joeji073/FD3S-DIGITAL-GAUGE-CLUSTER/FINAL_CENTER/gaugeassets2.h

// This file was generated with the command-line:
//    gd3asset -o gaugeassets2.h numberfont.ttf,size=70 numberfont2.ttf,size=25 GAUGENEEDLE.png,format=ARGB1555 REDNEEDLE.png,format=ARGB1555

#define NUMBERFONT_HANDLE 0
#define NUMBERFONT_WIDTH 71
#define NUMBERFONT_HEIGHT 77
#define NUMBERFONT_CELLS 96
#define NUMBERFONT2_HANDLE 1
#define NUMBERFONT2_WIDTH 26
#define NUMBERFONT2_HEIGHT 28
#define NUMBERFONT2_CELLS 96
#define GAUGENEEDLE_HANDLE 2
#define GAUGENEEDLE_WIDTH 70
#define GAUGENEEDLE_HEIGHT 70
#define GAUGENEEDLE_CELLS 1
#define REDNEEDLE_HANDLE 3
#define REDNEEDLE_WIDTH 90
#define REDNEEDLE_HEIGHT 25
#define REDNEEDLE_CELLS 1
#define ASSETS_END 315652UL
static const PROGMEM uint8_t __assets[31408] = {
0, 0, 0, 5, 0, 0, 0, 1, 77, 142, 0, 8, 0, 0, 0, 41, 77, 72, 16, 7, 0,
0, 0, 40, 128, 165, 126, 1, 43, 255, 255, 255, 0, 0, 0, 0, 128, 15, 4,
0, 1, 0, 0, 5, 20, 16, 4, 1, 28, 52, 0, 8, 0, 0, 0, 41, 28, 26, 16, 7,
0, 0, 0, 40, 148, 226, 3, 1, 43, 255, 255, 255, 1, 0, 0, 0, 148, 152,
4, 0, 2, 0, 0, 5, 40, 153, 4, 1, 70, 140, 0, 8, 0, 0, 0, 41, 70, 24,
1, 7, 0, 0, 0, 40, 3, 0, 0, 5, 112, 191, 4, 1, 25, 180, 0, 8, 0, 0, 0,
41, 25, 104, 1, 7, 0, 0, 0, 40, 34, 255, 255, 255, 0, 0, 0, 0, 120,
218, 236, 189, 9, 124, 108, 89, 85, 47, 92, 243, 92, 149, 92, 102,
186, 233, 36, 52, 32, 131, 244, 173, 56, 32, 126, 63, 164, 43, 248,
176, 197, 169, 43, 234, 19, 81, 180, 43, 190, 135, 162, 50, 84, 84,
236, 198, 207, 39, 21, 121, 14, 253, 4, 187, 130, 62, 249, 126, 202,
80, 1, 31, 138, 19, 21, 158, 126, 8, 10, 93, 1, 69, 6, 219, 174, 0,
234, 99, 250, 186, 210, 221, 50, 116, 55, 247, 158, 123, 111, 110,
110, 134, 74, 234, 124, 103, 216, 211, 201, 61, 107, 128, 84, 135, 59,
156, 245, 107, 232, 206, 189, 59, 85, 231, 236, 189, 246, 90, 255,
245, 95, 107, 175, 29, 139, 69, 18, 73, 36, 145, 68, 18, 73, 36, 145,
68, 18, 73, 36, 151, 172, 100, 108, 71, 246, 25, 99, 118, 241, 49, 89,
119, 204, 5, 198, 152, 243, 248, 152, 156, 59, 230, 44, 99, 204, 58,
62, 38, 239, 142, 89, 97, 140, 89, 196, 199, 20, 220, 49, 115, 140,
49, 51, 248, 152, 162, 51, 100, 20, 163, 199, 12, 137, 49, 37, 103,
204, 14, 99, 204, 22, 49, 166, 236, 140, 57, 199, 24, 179, 65, 140,
169, 56, 99, 214, 24, 99, 150, 137, 49, 19, 206, 152, 5, 198, 152, 89,
98, 204, 52, 61, 205, 238, 152, 125, 106, 76, 213, 182, 247, 24, 99,
182, 169, 49, 53, 82, 227, 189, 49, 103, 169, 49, 117, 82, 227, 189,
49, 43, 212, 152, 6, 169, 241, 222, 152, 121, 106, 76, 147, 212, 120,
119, 12, 185, 20, 177, 22, 169, 241, 238, 152, 29, 114, 76, 155, 212,
120, 119, 204, 38, 57, 166, 67, 106, 188, 59, 102, 141, 28, 211, 37,
53, 222, 29, 179, 64, 142, 233, 145, 26, 239, 142, 153, 36, 199, 244,
15, 46, 55, 207, 212, 178, 105, 147, 208, 113, 199, 204, 83, 179, 76,
155, 141, 62, 195, 130, 15, 220, 49, 196, 51, 91, 206, 16, 98, 162,
227, 12, 135, 155, 116, 199, 16, 230, 39, 205, 112, 202, 158, 227,
222, 142, 69, 18, 201, 213, 36, 30, 62, 156, 75, 185, 255, 191, 132,
97, 182, 145, 191, 65, 102, 49, 60, 182, 231, 161, 214, 17, 138, 145,
182, 60, 36, 185, 139, 226, 159, 123, 189, 111, 220, 194, 48, 137,
189, 234, 33, 183, 123, 49, 188, 225, 24, 196, 178, 55, 18, 193, 0,
142, 33, 195, 209, 84, 211, 51, 64, 85, 212, 228, 181, 60, 152, 89,
67, 77, 149, 99, 125, 55, 61, 180, 176, 131, 90, 223, 117, 239, 27,
55, 81, 235, 187, 236, 122, 103, 12, 225, 12, 60, 59, 223, 65, 129,
164, 229, 173, 83, 15, 195, 235, 113, 223, 174, 14, 48, 100, 146, 244,
3, 25, 11, 179, 192, 105, 15, 178, 197, 209, 144, 39, 227, 33, 227, 4,
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
};
#define LOAD_ASSETS()  (GD.copy(__assets, sizeof(__assets)), GD.loadptr = ASSETS_END)
static const shape_t NUMBERFONT_SHAPE = {0, 71, 77, 0};
static const shape_t NUMBERFONT2_SHAPE = {1, 26, 28, 0};
static const shape_t GAUGENEEDLE_SHAPE = {2, 70, 70, 0};
static const shape_t REDNEEDLE_SHAPE = {3, 90, 25, 0};
struct {
  Bitmap numberfont;
  Bitmap numberfont2;
  Bitmap gaugeneedle;
  Bitmap redneedle;
} bitmaps = {
 /*       numberfont */  {{ 71,  77}, { 35,  38},      0x0UL,  2,  0},
 /*      numberfont2 */  {{ 26,  28}, { 13,  14},  0x41014UL,  2,  1},
 /*      gaugeneedle */  {{ 70,  70}, { 35,  35},  0x49928UL,  0,  2},
 /*        redneedle */  {{ 90,  25}, { 45,  12},  0x4bf70UL,  0,  3}
};
