joeji073/FD3S-DIGITAL-GAUGE-CLUSTER/FINAL_LEFT_BOTTOM/leftasset.h

// This file was generated with the command-line:
//    gd3asset -o leftasset.h numberfont.ttf,size=42 numberfont2.ttf,size=80 leftgaugecenter.png,format=ARGB1555

#define NUMBERFONT_HANDLE 0
#define NUMBERFONT_WIDTH 43
#define NUMBERFONT_HEIGHT 49
#define NUMBERFONT_CELLS 96
#define NUMBERFONT2_HANDLE 1
#define NUMBERFONT2_WIDTH 82
#define NUMBERFONT2_HEIGHT 88
#define NUMBERFONT2_CELLS 96
#define LEFTGAUGECENTER_HANDLE 2
#define LEFTGAUGECENTER_WIDTH 36
#define LEFTGAUGECENTER_HEIGHT 36
#define LEFTGAUGECENTER_CELLS 1
#define ASSETS_END 452744UL
static const PROGMEM uint8_t __assets[40160] = {
0, 0, 0, 5, 0, 0, 0, 1, 49, 86, 0, 8, 0, 0, 0, 41, 49, 44, 16, 7, 0,
0, 0, 40, 64, 121, 127, 1, 43, 255, 255, 255, 0, 0, 0, 0, 64, 148, 1,
0, 1, 0, 0, 5, 212, 148, 1, 1, 88, 164, 0, 8, 0, 0, 0, 41, 88, 82, 16,
7, 0, 0, 0, 40, 212, 209, 127, 1, 43, 255, 255, 255, 1, 0, 0, 0, 212,
221, 6, 0, 2, 0, 0, 5, 104, 222, 6, 1, 36, 72, 0, 8, 0, 0, 0, 41, 36,
144, 0, 7, 0, 0, 0, 40, 34, 255, 255, 255, 0, 0, 0, 0, 120, 218, 236,
189, 11, 156, 108, 87, 89, 39, 90, 239, 119, 85, 55, 144, 144, 128,
164, 187, 13, 247, 162, 8, 156, 106, 197, 43, 232, 149, 84, 43, 199,
145, 81, 73, 53, 222, 31, 242, 210, 84, 227, 252, 46, 94, 24, 76, 53,
56, 206, 204, 213, 33, 117, 96, 192, 241, 250, 160, 26, 189, 48, 63,
175, 152, 106, 24, 20, 127, 254, 2, 213, 48, 160, 48, 99, 168, 70, 30,
2, 146, 84, 7, 228, 161, 137, 167, 250, 16, 146, 16, 146, 211, 149,
115, 78, 191, 31, 181, 239, 94, 107, 191, 214, 94, 235, 219, 223, 250,
58, 167, 155, 243, 200, 250, 52, 1, 246, 89, 167, 246, 94, 107, 125,
143, 255, 247, 88, 223, 138, 197, 12, 25, 50, 100, 232, 178, 166, 172,
101, 237, 130, 79, 183, 212, 167, 57, 203, 90, 7, 159, 158, 83, 159,
230, 45, 107, 5, 124, 186, 168, 62, 45, 88, 214, 41, 240, 233, 172,
250, 180, 104, 89, 83, 208, 211, 17, 48, 183, 146, 181, 7, 62, 221, 6,
158, 150, 173, 77, 240, 233, 5, 224, 105, 197, 90, 5, 159, 46, 131,
79, 23, 128, 167, 99, 214, 28, 240, 116, 210, 154, 1, 159, 142, 3, 79,
171, 7, 208, 110, 86, 119, 161, 167, 181, 45, 240, 233, 58, 244, 180,
126, 30, 124, 186, 122, 145, 108, 214, 178, 160, 25, 119, 192, 45,
238, 89, 214, 180, 250, 180, 15, 110, 252, 208, 178, 128, 183, 89,
214, 129, 145, 236, 227, 36, 91, 230, 23, 171, 214, 104, 92, 145, 216,
185, 186, 34, 115, 182, 108, 142, 55, 21, 117, 82, 182, 199, 181, 172,
243, 138, 180, 108, 217, 76, 177, 162, 72, 192, 249, 88, 87, 81, 17,
85, 123, 92, 95, 225, 148, 186, 61, 110, 160, 40, 131, 166, 45, 89,
214, 142, 194, 148, 163, 88, 194, 218, 80, 152, 114, 55, 150, 84, 5,
188, 187, 17, 75, 91, 75, 102, 231, 13, 25, 186, 8, 234, 217, 66, 219,
83, 12, 229, 208, 54, 146, 67, 89, 192, 147, 182, 113, 72, 42, 6, 194,
70, 38, 227, 236, 31, 89, 199, 28, 216, 255, 236, 43, 218, 100, 199,
254, 71, 182, 246, 53, 91, 228, 107, 10, 144, 105, 217, 32, 166, 101,
157, 33, 124, 174, 109, 180, 28, 90, 144, 140, 150, 67, 243, 226, 211,
129, 247, 116, 78, 50, 90, 14, 133, 204, 253, 201, 134, 181, 203, 255,
25, 7, 62, 119, 67, 81, 104, 231, 237, 127, 206, 41, 246, 116, 197,
86, 148, 178, 250, 28, 216, 152, 107, 32, 225, 174, 188, 247, 9, 59,
18, 184, 114, 104, 43, 172, 170, 93, 218, 8, 47, 174, 75, 161, 149,
76, 121, 147, 248, 41, 73, 43, 175, 243, 127, 160, 53, 151, 39, 209,
69, 88, 68, 194, 82, 9, 123, 97, 85, 22, 201, 216, 72, 33, 163, 160,
133, 188, 13, 17, 243, 10, 76, 44, 217, 232, 183, 172, 32, 224, 73,
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
};
#define LOAD_ASSETS()  (GD.copy(__assets, sizeof(__assets)), GD.loadptr = ASSETS_END)
static const shape_t NUMBERFONT_SHAPE = {0, 43, 49, 0};
static const shape_t NUMBERFONT2_SHAPE = {1, 82, 88, 0};
static const shape_t LEFTGAUGECENTER_SHAPE = {2, 36, 36, 0};
struct {
  Bitmap numberfont;
  Bitmap numberfont2;
  Bitmap leftgaugecenter;
} bitmaps = {
 /*       numberfont */  {{ 43,  49}, { 21,  24},      0x0UL,  2,  0},
 /*      numberfont2 */  {{ 82,  88}, { 41,  44},  0x194d4UL,  2,  1},
 /*  leftgaugecenter */  {{ 36,  36}, { 18,  18},  0x6de68UL,  0,  2}
};
