joeji073/FD3S-DIGITAL-GAUGE-CLUSTER/FINAL_RIGHT/rightassets.h

// This file was generated with the command-line:
//    gd3asset -o rightassets.h numberfont.ttf,size=70 rightneedle.png,format=ARGB1555

#define NUMBERFONT_HANDLE 0
#define NUMBERFONT_WIDTH 71
#define NUMBERFONT_HEIGHT 77
#define NUMBERFONT_CELLS 96
#define RIGHTNEEDLE_HANDLE 1
#define RIGHTNEEDLE_WIDTH 45
#define RIGHTNEEDLE_HEIGHT 45
#define RIGHTNEEDLE_CELLS 1
#define ASSETS_END 270310UL
static const PROGMEM uint8_t __assets[23700] = {
0, 0, 0, 5, 0, 0, 0, 1, 77, 142, 0, 8, 0, 0, 0, 41, 77, 72, 16, 7, 0,
0, 0, 40, 128, 165, 126, 1, 43, 255, 255, 255, 0, 0, 0, 0, 128, 15, 4,
0, 1, 0, 0, 5, 20, 16, 4, 1, 45, 90, 0, 8, 0, 0, 0, 41, 45, 180, 0, 7,
0, 0, 0, 40, 34, 255, 255, 255, 0, 0, 0, 0, 120, 218, 237, 189, 11,
156, 164, 87, 85, 47, 90, 239, 119, 85, 247, 240, 148, 132, 76, 119,
194, 43, 32, 153, 106, 84, 196, 251, 83, 82, 13, 71, 35, 68, 73, 53,
120, 110, 124, 29, 83, 125, 15, 40, 42, 143, 106, 21, 19, 188, 106,
170, 229, 23, 143, 220, 67, 78, 170, 227, 131, 43, 7, 164, 58, 120,
162, 224, 37, 212, 228, 30, 241, 144, 115, 73, 170, 141, 135, 168, 57,
30, 106, 16, 244, 168, 112, 83, 157, 68, 8, 9, 102, 190, 201, 244,
244, 244, 187, 190, 91, 223, 126, 125, 95, 85, 127, 235, 145, 116,
101, 238, 244, 204, 94, 243, 19, 130, 89, 179, 107, 127, 123, 175,
189, 214, 127, 255, 247, 218, 107, 71, 34, 86, 172, 88, 177, 98, 197,
138, 21, 43, 86, 172, 88, 57, 111, 37, 229, 14, 100, 151, 161, 179,
133, 235, 164, 61, 157, 179, 12, 157, 51, 184, 78, 198, 211, 121, 138,
161, 115, 2, 215, 201, 122, 58, 203, 12, 157, 5, 92, 39, 231, 233,
204, 50, 116, 166, 113, 157, 252, 64, 165, 31, 161, 117, 118, 8, 157,
194, 64, 103, 147, 161, 179, 78, 232, 20, 7, 58, 167, 25, 58, 171,
132, 78, 105, 160, 179, 194, 208, 89, 34, 116, 38, 6, 58, 243, 12,
157, 25, 66, 103, 138, 30, 102, 79, 103, 151, 210, 41, 187, 238, 54,
67, 103, 131, 210, 169, 144, 22, 47, 116, 158, 162, 116, 170, 164,
197, 11, 157, 101, 74, 167, 70, 90, 188, 208, 153, 163, 116, 234, 164,
197, 123, 58, 228, 84, 68, 26, 164, 197, 123, 58, 155, 164, 78, 147,
180, 120, 79, 103, 141, 212, 105, 145, 22, 239, 233, 172, 144, 58,
109, 210, 226, 61, 157, 121, 82, 167, 67, 90, 188, 167, 51, 73, 234,
116, 247, 14, 91, 100, 106, 184, 180, 75, 104, 121, 58, 115, 212, 40,
211, 110, 163, 203, 240, 224, 61, 79, 135, 232, 179, 51, 80, 33, 6,
58, 202, 8, 184, 113, 79, 135, 112, 63, 73, 70, 80, 22, 129, 123, 35,
98, 197, 202, 197, 36, 2, 31, 206, 38, 188, 255, 92, 196, 48, 91, 95,
46, 144, 25, 12, 143, 109, 11, 212, 218, 71, 49, 210, 186, 64, 146,
91, 40, 254, 121, 88, 252, 226, 58, 134, 73, 220, 227, 2, 185, 61,
140, 225, 141, 129, 67, 44, 10, 77, 4, 3, 12, 28, 25, 142, 166, 234,
194, 1, 149, 81, 151, 215, 16, 48, 179, 130, 186, 170, 129, 247, 93,
19, 104, 97, 19, 245, 190, 39, 196, 47, 174, 161, 222, 119, 201, 139,
206, 24, 194, 233, 9, 63, 223, 66, 129, 164, 35, 230, 169, 131, 225,
245, 168, 244, 171, 61, 12, 153, 196, 229, 70, 198, 193, 60, 112, 82,
64, 182, 40, 186, 229, 73, 9, 100, 28, 67, 193, 93, 70, 192, 177, 132,
203, 64, 20, 86, 172, 88, 177, 98, 197, 138, 149, 139, 81, 60, 36,
186, 38, 129, 219, 2, 134, 107, 87, 5, 40, 131, 81, 144, 66, 144, 45,
12, 215, 150, 37, 120, 238, 98, 0, 176, 38, 55, 223, 14, 134, 125, 7,
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
};
#define LOAD_ASSETS()  (GD.copy(__assets, sizeof(__assets)), GD.loadptr = ASSETS_END)
static const shape_t NUMBERFONT_SHAPE = {0, 71, 77, 0};
static const shape_t RIGHTNEEDLE_SHAPE = {1, 45, 45, 0};
struct {
  Bitmap numberfont;
  Bitmap rightneedle;
} bitmaps = {
 /*       numberfont */  {{ 71,  77}, { 35,  38},      0x0UL,  2,  0},
 /*      rightneedle */  {{ 45,  45}, { 22,  22},  0x41014UL,  0,  1}
};
